bemcgarvey/SAMD21Demo/firmware/MSD-SPI/firmware/src/config/default/peripheral/sercom/spi_master/plib_sercom0_spi_master.c

/*******************************************************************************
  SERIAL COMMUNICATION SERIAL PERIPHERAL INTERFACE(SERCOM0_SPI) PLIB

  Company
    Microchip Technology Inc.

  File Name
    plib_sercom0_spi_master.c

  Summary
    SERCOM0_SPI Master PLIB Implementation File.

  Description
    This file defines the interface to the SERCOM SPI peripheral library.
    This library provides access to and control of the associated
    peripheral instance.

  Remarks:
    None.

*******************************************************************************/

// DOM-IGNORE-BEGIN
/*******************************************************************************
* Copyright (C) 2018 Microchip Technology Inc. and its subsidiaries.
*
* Subject to your compliance with these terms, you may use Microchip software
* and any derivatives exclusively with Microchip products. It is your
* responsibility to comply with third party license terms applicable to your
* use of third party software (including open source software) that may
* accompany Microchip software.
*
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
* IN NO EVENT WILL MICROCHIP BE LIABLE FOR ANY INDIRECT, SPECIAL, PUNITIVE,
* INCIDENTAL OR CONSEQUENTIAL LOSS, DAMAGE, COST OR EXPENSE OF ANY KIND
* WHATSOEVER RELATED TO THE SOFTWARE, HOWEVER CAUSED, EVEN IF MICROCHIP HAS
* BEEN ADVISED OF THE POSSIBILITY OR THE DAMAGES ARE FORESEEABLE. TO THE
* FULLEST EXTENT ALLOWED BY LAW, MICROCHIP'S TOTAL LIABILITY ON ALL CLAIMS IN
* ANY WAY RELATED TO THIS SOFTWARE WILL NOT EXCEED THE AMOUNT OF FEES, IF ANY,
* THAT YOU HAVE PAID DIRECTLY TO MICROCHIP FOR THIS SOFTWARE.
*******************************************************************************/
// DOM-IGNORE-END

#include "interrupts.h"
#include "plib_sercom0_spi_master.h"

// *****************************************************************************
// *****************************************************************************
// Section: MACROS Definitions
// *****************************************************************************
// *****************************************************************************


/* SERCOM0 clk freq value for the baud calculation */
#define SERCOM0_Frequency      (48000000UL)

/* SERCOM0 SPI baud value for 5000000 Hz baud rate */
#define SERCOM0_SPIM_BAUD_VALUE         (3UL)

/*Global object to save SPI Exchange related data  */
static SPI_OBJECT sercom0SPIObj;

// *****************************************************************************
// *****************************************************************************
// Section: SERCOM0_SPI Implementation
// *****************************************************************************
// *****************************************************************************
// *****************************************************************************

// *****************************************************************************
/* Function:
    void SERCOM0_SPI_Initialize(void);

  Summary:
    Initializes instance SERCOM0 of the SERCOM module operating in SPI mode.

  Description:
    This function initializes instance SERCOM0 of SERCOM module operating in SPI mode.
    This function should be called before any other library function. The SERCOM
    module will be configured as per the MHC settings.

  Remarks:
    Refer plib_sercom0_spi.h file for more information.
*/

void SERCOM0_SPI_Initialize(void)
{
    /* Instantiate the SERCOM0 SPI object */
    sercom0SPIObj.callback = NULL ;
    sercom0SPIObj.transferIsBusy = false ;
    sercom0SPIObj.txSize = 0U;
    sercom0SPIObj.rxSize = 0U;

    /* Selection of the Character Size and Receiver Enable */
    SERCOM0_REGS->SPIM.SERCOM_CTRLB = SERCOM_SPIM_CTRLB_CHSIZE_8_BIT | SERCOM_SPIM_CTRLB_RXEN_Msk ;

    /* Wait for synchronization */
    while((SERCOM0_REGS->SPIM.SERCOM_SYNCBUSY) != 0U)
    {
        /* Do nothing */
    }

    /* Selection of the Baud Value */
    SERCOM0_REGS->SPIM.SERCOM_BAUD = (uint8_t)SERCOM_SPIM_BAUD_BAUD(SERCOM0_SPIM_BAUD_VALUE);

    /* Configure Data Out Pin Out , Master Mode,
     * Data In and Pin Out,Data Order and Standby mode if configured
     * and Selection of the Clock Phase and Polarity and Enable the SPI Module
     */
    SERCOM0_REGS->SPIM.SERCOM_CTRLA = SERCOM_SPIM_CTRLA_MODE_SPI_MASTER | SERCOM_SPIM_CTRLA_DOPO_PAD0 | SERCOM_SPIM_CTRLA_DIPO_PAD2 | SERCOM_SPIM_CTRLA_CPOL_IDLE_LOW | SERCOM_SPIM_CTRLA_CPHA_LEADING_EDGE | SERCOM_SPIM_CTRLA_DORD_MSB | SERCOM_SPIM_CTRLA_ENABLE_Msk ;


    /* Wait for synchronization */
    while((SERCOM0_REGS->SPIM.SERCOM_SYNCBUSY) != 0U)
    {
        /* Do nothing */
    }
}

// *****************************************************************************
/* Function:
    bool SERCOM0_SPI_TransferSetup(SPI_TRANSFER_SETUP *setup,
                                                uint32_t spiSourceClock);

 Summary:
    Configure SERCOM SPI operational parameters at run time.

  Description:
    This function allows the application to change the SERCOM SPI operational
    parameter at run time. The application can thus override the MHC defined
    configuration for these parameters. The parameter are specified via the
    SPI_TRANSFER_SETUP type setup parameter. Each member of this parameter
    should be initialized to the desired value.

    The application may feel need to call this function in situation where
    multiple SPI slaves, each with different operation parameters, are connected
    to one SPI master. This function can thus be used to setup the SPI Master to
    meet the communication needs of the slave.

    Calling this function will affect any ongoing communication. The application
    must thus ensure that there is no on-going communication on the SPI before
    calling this function.

  Remarks:
    Refer plib_sercom0_spi.h file for more information.
*/

bool SERCOM0_SPI_TransferSetup(SPI_TRANSFER_SETUP *setup, uint32_t spiSourceClock)
{
    uint32_t baudValue = 0U;

    bool statusValue = false;

    if(spiSourceClock == 0U)
    {
        /* Fetch Master Clock Frequency directly */
        spiSourceClock = SERCOM0_Frequency;
    }

    /* Disable the SPI Module */
    SERCOM0_REGS->SPIM.SERCOM_CTRLA &= ~(SERCOM_SPIM_CTRLA_ENABLE_Msk);

    /* Wait for synchronization */
    while((SERCOM0_REGS->SPIM.SERCOM_SYNCBUSY) != 0U)
    {
        /* Do nothing */
    }

    if(setup != NULL)
    {
        baudValue = (spiSourceClock/(2U*(setup->clockFrequency))) - 1U;

        if((baudValue > 0U) && (baudValue <= 255U))
        {
            /* Selection of the Clock Polarity and Clock Phase */
            SERCOM0_REGS->SPIM.SERCOM_CTRLA &= ~(SERCOM_SPIM_CTRLA_CPOL_Msk | SERCOM_SPIM_CTRLA_CPHA_Msk);
            SERCOM0_REGS->SPIM.SERCOM_CTRLA |= (uint32_t)setup->clockPolarity | (uint32_t)setup->clockPhase;

            /* Selection of the Baud Value */
            SERCOM0_REGS->SPIM.SERCOM_BAUD = (uint8_t)baudValue;

            /* Selection of the Character Size */
            SERCOM0_REGS->SPIM.SERCOM_CTRLB &= ~SERCOM_SPIM_CTRLB_CHSIZE_Msk;
            SERCOM0_REGS->SPIM.SERCOM_CTRLB |= (uint32_t)setup->dataBits;

            /* Wait for synchronization */
            while((SERCOM0_REGS->SPIM.SERCOM_SYNCBUSY) != 0U)
            {
                /* Do nothing */
            }

            statusValue = true;
        }
    }

    /* Enabling the SPI Module */
    SERCOM0_REGS->SPIM.SERCOM_CTRLA |= SERCOM_SPIM_CTRLA_ENABLE_Msk;

    /* Wait for synchronization */
    while((SERCOM0_REGS->SPIM.SERCOM_SYNCBUSY) != 0U)
    {
        /* Do nothing */
    }

    return statusValue;
}


// *****************************************************************************
/* Function:
    void SERCOM0_SPI_CallbackRegister(const SERCOM_SPI_CALLBACK* callBack,
                                                    uintptr_t context);

  Summary:
    Allows application to register callback with PLIB.

  Description:
    This function allows application to register an event handling function
    for the PLIB to call back when requested data exchange operation has
    completed or any error has occurred.
    The callback should be registered before the client performs exchange
    operation.
    At any point if application wants to stop the callback, it can use this
    function with "callBack" value as NULL.

  Remarks:
    Refer plib_sercom0_spi.h file for more information.
*/

void SERCOM0_SPI_CallbackRegister(SERCOM_SPI_CALLBACK callBack, uintptr_t context )
{
    sercom0SPIObj.callback = callBack;

    sercom0SPIObj.context = context;
}

// *****************************************************************************
/* Function:
    bool SERCOM0_SPI_IsBusy(void);

  Summary:
    Returns transfer status of SERCOM SERCOM0SPI.

  Description:
    This function ture if the SERCOM SERCOM0SPI module is busy with a transfer. The
    application can use the function to check if SERCOM SERCOM0SPI module is busy
    before calling any of the data transfer functions. The library does not
    allow a data transfer operation if another transfer operation is already in
    progress.

    This function can be used as an alternative to the callback function when
    the library is operating interrupt mode. The allow the application to
    implement a synchronous interface to the library.

  Remarks:
    Refer plib_sercom0_spi.h file for more information.
*/

bool SERCOM0_SPI_IsBusy(void)
{
    bool isBusy = false;
	if ((sercom0SPIObj.txSize == 0U) && (sercom0SPIObj.rxSize == 0U))
	{
		/* This means no transfer has been requested yet; hence SPI is not busy. */
		isBusy = false;
	}
	else
	{
        /* if transmit is not complete or if the state flag is not set, SPI is busy */
        isBusy = (((SERCOM0_REGS->SPIM.SERCOM_INTFLAG & SERCOM_SPIM_INTFLAG_TXC_Msk) == 0U) || sercom0SPIObj.transferIsBusy);
	}
    return isBusy;
}

bool SERCOM0_SPI_IsTransmitterBusy(void)
{
    return ((SERCOM0_REGS->SPIM.SERCOM_INTFLAG & SERCOM_SPIM_INTFLAG_TXC_Msk) == 0)? true : false;
}

// *****************************************************************************
/* Function:
    bool SERCOM0_SPI_WriteRead (void* pTransmitData, size_t txSize
                                        void* pReceiveData, size_t rxSize);

  Summary:
    Write and Read data on SERCOM SERCOM0 SPI peripheral.

  Description:
    This function transmits "txSize" number of bytes and receives "rxSize"
    number of bytes on SERCOM SERCOM0 SPI module. Data pointed by pTransmitData is
    transmitted and received data is saved in the location pointed by
    pReceiveData. The function will transfer the maximum of "txSize" or "rxSize"
    data units towards completion.

    When "Interrupt Mode" option is unchecked in MHC, this function will be
    blocking in nature.  In this mode, the function will not return until all
    the requested data is transferred.  The function returns true after
    transferring all the data.  This indicates that the operation has been
    completed.

    When "Interrupt Mode" option is selected in MHC, the function will be
    non-blocking in nature.  The function returns immediately. The data transfer
    process continues in the peripheral interrupt.  The application specified
    transmit and receive buffer  are ownerd by the library until the data
    transfer is complete and should not be modified by the application till the
    transfer is complete.  Only one transfer is allowed at any time. The
    Application can use a callback function or a polling function to check for
    completion of the transfer. If a callback is required, this should be
    registered prior to calling the SERCOM0_SPI_WriteRead() function. The
    application can use the SERCOM0_SPI_IsBusy() to poll for completion.

  Remarks:
    Refer plib_sercom0_spi.h file for more information.
*/

bool SERCOM0_SPI_WriteRead (void* pTransmitData, size_t txSize, void* pReceiveData, size_t rxSize)
{
    bool isRequestAccepted = false;
    uint32_t dummyData = 0U;

    /* Verify the request */
    if((((txSize > 0U) && (pTransmitData != NULL)) || ((rxSize > 0U) && (pReceiveData != NULL))) && (sercom0SPIObj.transferIsBusy == false))
    {
        if((SERCOM0_REGS->SPIM.SERCOM_CTRLB & SERCOM_SPIM_CTRLB_CHSIZE_Msk) == (uint32_t)SPI_DATA_BITS_9)
        {
            /* For 9-bit transmission, the txSize and rxSize must be an even number. */
            if(((txSize > 0U) && ((txSize & 0x01U) != 0U)) || ((rxSize > 0U) && ((rxSize & 0x01U) != 0U)))
            {
                return isRequestAccepted;
            }
        }

        isRequestAccepted = true;
        sercom0SPIObj.txBuffer = pTransmitData;
        sercom0SPIObj.rxBuffer = pReceiveData;
        sercom0SPIObj.rxCount = 0U;
        sercom0SPIObj.txCount = 0U;
        sercom0SPIObj.dummySize = 0U;

        if(pTransmitData != NULL)
        {
            sercom0SPIObj.txSize = txSize;
        }
        else
        {
            sercom0SPIObj.txSize = 0U;
        }

        if(pReceiveData != NULL)
        {
            sercom0SPIObj.rxSize = rxSize;
        }
        else
        {
            sercom0SPIObj.rxSize = 0U;
        }

        sercom0SPIObj.transferIsBusy = true;

        /* Flush out any unread data in SPI read buffer */
        while((SERCOM0_REGS->SPIM.SERCOM_INTFLAG & SERCOM_SPIM_INTFLAG_RXC_Msk) == SERCOM_SPIM_INTFLAG_RXC_Msk)
        {
            dummyData = SERCOM0_REGS->SPIM.SERCOM_DATA;
            (void)dummyData;
        }

        SERCOM0_REGS->SPIM.SERCOM_STATUS |= (uint16_t)SERCOM_SPIM_STATUS_BUFOVF_Msk;

        SERCOM0_REGS->SPIM.SERCOM_INTFLAG |= (uint8_t)SERCOM_SPIM_INTFLAG_ERROR_Msk;

        if(sercom0SPIObj.rxSize > sercom0SPIObj.txSize)
        {
            sercom0SPIObj.dummySize = sercom0SPIObj.rxSize - sercom0SPIObj.txSize;
        }

        /* Start the first write here itself, rest will happen in ISR context */
        if((SERCOM0_REGS->SPIM.SERCOM_CTRLB & SERCOM_SPIM_CTRLB_CHSIZE_Msk) == (uint32_t)SPI_DATA_BITS_8)
        {
            if(sercom0SPIObj.txCount < sercom0SPIObj.txSize)
            {
                SERCOM0_REGS->SPIM.SERCOM_DATA = *((uint8_t*)sercom0SPIObj.txBuffer);

                sercom0SPIObj.txCount++;
            }
            else if(sercom0SPIObj.dummySize > 0U)
            {
                SERCOM0_REGS->SPIM.SERCOM_DATA = 0xFFU;

                sercom0SPIObj.dummySize--;
            }
            else
            {
                /* Do nothing */
            }
        }
        else
        {
            sercom0SPIObj.txSize >>= 1U;
            sercom0SPIObj.dummySize >>= 1U;
            sercom0SPIObj.rxSize >>= 1U;

            if(sercom0SPIObj.txCount < sercom0SPIObj.txSize)
            {
                SERCOM0_REGS->SPIM.SERCOM_DATA = *((uint16_t*)sercom0SPIObj.txBuffer) & SERCOM_SPIM_DATA_Msk;

                sercom0SPIObj.txCount++;
            }
            else if(sercom0SPIObj.dummySize > 0U)
            {
                SERCOM0_REGS->SPIM.SERCOM_DATA = 0xFFFFU & SERCOM_SPIM_DATA_Msk;

                sercom0SPIObj.dummySize--;
            }
            else
            {
                /* Do nothing */
            }
        }

        if(rxSize > 0U)
        {
            /* Enable ReceiveComplete  */
            SERCOM0_REGS->SPIM.SERCOM_INTENSET = (uint8_t)SERCOM_SPIM_INTENSET_RXC_Msk;
        }
        else
        {
            /* Enable the DataRegisterEmpty  */
            SERCOM0_REGS->SPIM.SERCOM_INTENSET = (uint8_t)SERCOM_SPIM_INTENSET_DRE_Msk;
        }
    }

    return isRequestAccepted;
}

bool SERCOM0_SPI_Write(void* pTransmitData, size_t txSize)
{
    return SERCOM0_SPI_WriteRead(pTransmitData, txSize, NULL, 0U);
}

bool SERCOM0_SPI_Read(void* pReceiveData, size_t rxSize)
{
    return SERCOM0_SPI_WriteRead(NULL, 0U, pReceiveData, rxSize);
}

// *****************************************************************************
/* Function:
    void SERCOM0_SPI_InterruptHandler(void);

  Summary:
    Handler that handles the SPI interrupts

  Description:
    This Function is called from the handler to handle the exchange based on the
    Interrupts.

  Remarks:
    Refer plib_sercom0_spi.h file for more information.
*/

void SERCOM0_SPI_InterruptHandler(void)
{
    uint32_t dataBits = 0U;
    uint32_t receivedData = 0U;
    static bool isLastByteTransferInProgress = false;

    if(SERCOM0_REGS->SPIM.SERCOM_INTENSET != 0U)
    {
        dataBits = SERCOM0_REGS->SPIM.SERCOM_CTRLB & SERCOM_SPIM_CTRLB_CHSIZE_Msk;

        if((SERCOM0_REGS->SPIM.SERCOM_INTFLAG & SERCOM_SPIM_INTFLAG_RXC_Msk) == SERCOM_SPIM_INTFLAG_RXC_Msk)
        {
            receivedData =  SERCOM0_REGS->SPIM.SERCOM_DATA;

            if(sercom0SPIObj.rxCount < sercom0SPIObj.rxSize)
            {
                if(dataBits == (uint32_t)SPI_DATA_BITS_8)
                {
                    ((uint8_t*)sercom0SPIObj.rxBuffer)[sercom0SPIObj.rxCount++] = (uint8_t)receivedData;
                }
                else
                {
                    ((uint16_t*)sercom0SPIObj.rxBuffer)[sercom0SPIObj.rxCount++] = (uint16_t)receivedData;
                }
            }
        }

        /* If there are more words to be transmitted, then transmit them here and keep track of the count */
        if((SERCOM0_REGS->SPIM.SERCOM_INTFLAG & SERCOM_SPIM_INTFLAG_DRE_Msk) == SERCOM_SPIM_INTFLAG_DRE_Msk)
        {
            /* Disable the DRE interrupt. This will be enabled back if more than
             * one byte is pending to be transmitted */
            SERCOM0_REGS->SPIM.SERCOM_INTENCLR = (uint8_t)SERCOM_SPIM_INTENCLR_DRE_Msk;

            if(dataBits == (uint32_t)SPI_DATA_BITS_8)
            {
                if(sercom0SPIObj.txCount < sercom0SPIObj.txSize)
                {
                    SERCOM0_REGS->SPIM.SERCOM_DATA = ((uint8_t*)sercom0SPIObj.txBuffer)[sercom0SPIObj.txCount++];
                }
                else if(sercom0SPIObj.dummySize > 0U)
                {
                    SERCOM0_REGS->SPIM.SERCOM_DATA = 0xFFU;

                    sercom0SPIObj.dummySize--;
                }
                else
                {
                    /* Do nothing */
                }
            }
            else
            {
                if(sercom0SPIObj.txCount < sercom0SPIObj.txSize)
                {
                    SERCOM0_REGS->SPIM.SERCOM_DATA = ((uint16_t*)sercom0SPIObj.txBuffer)[sercom0SPIObj.txCount++];
                }
                else if(sercom0SPIObj.dummySize > 0U)
                {
                    SERCOM0_REGS->SPIM.SERCOM_DATA = 0xFFFFU;

                    sercom0SPIObj.dummySize--;
                }
                else
                {
                    /* Do nothing */
                }
            }

            if((sercom0SPIObj.txCount == sercom0SPIObj.txSize) && (sercom0SPIObj.dummySize == 0U))
            {
                 /* At higher baud rates, the data in the shift register can be
                 * shifted out and TXC flag can get set resulting in a
                 * callback been given to the application with the SPI interrupt
                 * pending with the application. This will then result in the
                 * interrupt handler being called again with nothing to transmit.
                 * To avoid this, a software flag is set, but
                 * the TXC interrupt is not enabled until the very end.
                 */

                isLastByteTransferInProgress = true;
            }
            else if(sercom0SPIObj.rxCount == sercom0SPIObj.rxSize)
            {
                SERCOM0_REGS->SPIM.SERCOM_INTENSET = (uint8_t)SERCOM_SPIM_INTENSET_DRE_Msk;

                SERCOM0_REGS->SPIM.SERCOM_INTENCLR = (uint8_t)SERCOM_SPIM_INTENCLR_RXC_Msk;
            }
            else
            {
                /* Do nothing */
            }
        }

        if(((SERCOM0_REGS->SPIM.SERCOM_INTFLAG & SERCOM_SPIM_INTFLAG_TXC_Msk) == SERCOM_SPIM_INTFLAG_TXC_Msk) && (isLastByteTransferInProgress == true))
        {
            if(sercom0SPIObj.rxCount == sercom0SPIObj.rxSize)
            {
                sercom0SPIObj.transferIsBusy = false;

                /* Disable the Data Register empty and Receive Complete Interrupt flags */
                SERCOM0_REGS->SPIM.SERCOM_INTENCLR = (uint8_t)(SERCOM_SPIM_INTENCLR_DRE_Msk | SERCOM_SPIM_INTENCLR_RXC_Msk | SERCOM_SPIM_INTENSET_TXC_Msk);

                isLastByteTransferInProgress = false;

                if(sercom0SPIObj.callback != NULL)
                {
                    sercom0SPIObj.callback(sercom0SPIObj.context);
                }
            }
        }

        if(isLastByteTransferInProgress == true)
        {
            /* For the last byte transfer, the DRE interrupt is already disabled.
             * Enable TXC interrupt to ensure no data is present in the shift
             * register before application callback is called.
             */
            SERCOM0_REGS->SPIM.SERCOM_INTENSET = (uint8_t)SERCOM_SPIM_INTENSET_TXC_Msk;
        }
    }
}
