bemcgarvey/SAMD21Demo/firmware/MSD-SPI/firmware/src/config/default/initialization.c

/*******************************************************************************
  System Initialization File

  File Name:
    initialization.c

  Summary:
    This file contains source code necessary to initialize the system.

  Description:
    This file contains source code necessary to initialize the system.  It
    implements the "SYS_Initialize" function, defines the configuration bits,
    and allocates any necessary global system resources,
 *******************************************************************************/

// DOM-IGNORE-BEGIN
/*******************************************************************************
* Copyright (C) 2018 Microchip Technology Inc. and its subsidiaries.
*
* Subject to your compliance with these terms, you may use Microchip software
* and any derivatives exclusively with Microchip products. It is your
* responsibility to comply with third party license terms applicable to your
* use of third party software (including open source software) that may
* accompany Microchip software.
*
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
* IN NO EVENT WILL MICROCHIP BE LIABLE FOR ANY INDIRECT, SPECIAL, PUNITIVE,
* INCIDENTAL OR CONSEQUENTIAL LOSS, DAMAGE, COST OR EXPENSE OF ANY KIND
* WHATSOEVER RELATED TO THE SOFTWARE, HOWEVER CAUSED, EVEN IF MICROCHIP HAS
* BEEN ADVISED OF THE POSSIBILITY OR THE DAMAGES ARE FORESEEABLE. TO THE
* FULLEST EXTENT ALLOWED BY LAW, MICROCHIP'S TOTAL LIABILITY ON ALL CLAIMS IN
* ANY WAY RELATED TO THIS SOFTWARE WILL NOT EXCEED THE AMOUNT OF FEES, IF ANY,
* THAT YOU HAVE PAID DIRECTLY TO MICROCHIP FOR THIS SOFTWARE.
 *******************************************************************************/
// DOM-IGNORE-END

// *****************************************************************************
// *****************************************************************************
// Section: Included Files
// *****************************************************************************
// *****************************************************************************
#include "configuration.h"
#include "definitions.h"
#include "device.h"



// ****************************************************************************
// ****************************************************************************
// Section: Configuration Bits
// ****************************************************************************
// ****************************************************************************
#pragma config NVMCTRL_BOOTPROT = SIZE_0BYTES
#pragma config NVMCTRL_EEPROM_SIZE = SIZE_0BYTES
#pragma config BOD33USERLEVEL = 0x7 // Enter Hexadecimal value
#pragma config BOD33_EN = ENABLED
#pragma config BOD33_ACTION = RESET

#pragma config BOD33_HYST = DISABLED
#pragma config NVMCTRL_REGION_LOCKS = 0xffff // Enter Hexadecimal value

#pragma config WDT_ENABLE = DISABLED
#pragma config WDT_ALWAYSON = DISABLED
#pragma config WDT_PER = CYC16384

#pragma config WDT_WINDOW_0 = SET
#pragma config WDT_WINDOW_1 = 0x4 // Enter Hexadecimal value
#pragma config WDT_EWOFFSET = CYC16384
#pragma config WDT_WEN = DISABLED




// *****************************************************************************
// *****************************************************************************
// Section: Driver Initialization Data
// *****************************************************************************
// *****************************************************************************
// <editor-fold defaultstate="collapsed" desc="DRV_MEMORY Instance 0 Initialization Data">


static DRV_MEMORY_CLIENT_OBJECT gDrvMemory0ClientObject[DRV_MEMORY_CLIENTS_NUMBER_IDX0];

static DRV_MEMORY_BUFFER_OBJECT gDrvMemory0BufferObject[DRV_MEMORY_BUFFER_QUEUE_SIZE_IDX0];

const DRV_MEMORY_DEVICE_INTERFACE drvMemory0DeviceAPI = {
    .Open               = DRV_AT25_Open,
    .Close              = DRV_AT25_Close,
    .Status             = DRV_AT25_Status,
    .SectorErase        = NULL,
    .Read               = DRV_AT25_Read,
    .PageWrite          = DRV_AT25_PageWrite,
    .EventHandlerSet    = NULL,
    .GeometryGet        = (DRV_MEMORY_DEVICE_GEOMETRY_GET)DRV_AT25_GeometryGet,
    .TransferStatusGet  = (DRV_MEMORY_DEVICE_TRANSFER_STATUS_GET)DRV_AT25_TransferStatusGet
};

const DRV_MEMORY_INIT drvMemory0InitData =
{
    .memDevIndex                = DRV_AT25_INDEX,
    .memoryDevice               = &drvMemory0DeviceAPI,
    .isMemDevInterruptEnabled   = false,
    .isFsEnabled                = false,
    .ewBuffer                   = NULL,
    .clientObjPool              = (uintptr_t)&gDrvMemory0ClientObject[0],
    .bufferObj                  = (uintptr_t)&gDrvMemory0BufferObject[0],
    .queueSize                  = DRV_MEMORY_BUFFER_QUEUE_SIZE_IDX0,
    .nClientsMax                = DRV_MEMORY_CLIENTS_NUMBER_IDX0
};

// </editor-fold>
// <editor-fold defaultstate="collapsed" desc="DRV_AT25 Initialization Data">

/* SPI PLIB Interface Initialization for AT25 Driver */
const DRV_AT25_PLIB_INTERFACE drvAT25PlibAPI = {

    /* SPI PLIB WriteRead function */
    .writeRead = (DRV_AT25_PLIB_WRITE_READ)SERCOM0_SPI_WriteRead,

    /* SPI PLIB Write function */
    .write = (DRV_AT25_PLIB_WRITE)SERCOM0_SPI_Write,

    /* SPI PLIB Read function */
    .read = (DRV_AT25_PLIB_READ)SERCOM0_SPI_Read,

    /* SPI PLIB Transfer Status function */
    .isBusy = (DRV_AT25_PLIB_IS_BUSY)SERCOM0_SPI_IsBusy,

    /* SPI PLIB Callback Register */
    .callbackRegister = (DRV_AT25_PLIB_CALLBACK_REGISTER)SERCOM0_SPI_CallbackRegister,
};

/* AT25 Driver Initialization Data */
const DRV_AT25_INIT drvAT25InitData =
{
    /* SPI PLIB API  interface*/
    .spiPlib = &drvAT25PlibAPI,

    /* AT25 Number of clients */
    .numClients = DRV_AT25_CLIENTS_NUMBER_IDX,

    /* EEPROM Page Size in bytes */
    .pageSize = DRV_AT25_EEPROM_PAGE_SIZE,

    /* Total size of the EEPROM in bytes */
    .flashSize = DRV_AT25_EEPROM_FLASH_SIZE,

    .blockStartAddress =    0x0,

    .chipSelectPin    = DRV_AT25_CHIP_SELECT_PIN_IDX,

    .holdPin    = DRV_AT25_HOLD_PIN_IDX,

    .writeProtectPin    = DRV_AT25_WP_PIN_IDX,
};

// </editor-fold>


// *****************************************************************************
// *****************************************************************************
// Section: System Data
// *****************************************************************************
// *****************************************************************************
/* Structure to hold the object handles for the modules in the system. */
SYSTEM_OBJECTS sysObj;

// *****************************************************************************
// *****************************************************************************
// Section: Library/Stack Initialization Data
// *****************************************************************************
// *****************************************************************************
/******************************************************
 * USB Driver Initialization
 ******************************************************/
 
/*  When designing a Self-powered USB Device, the application should make sure
    that USB_DEVICE_Attach() function is called only when VBUS is actively powered.
	Therefore, the firmware needs some means to detect when the Host is powering 
	the VBUS. A 5V tolerant I/O pin can be connected to VBUS (through a resistor)
	and can be used to detect when VBUS is high or low. The application can specify
	a VBUS Detect function through the USB Driver Initialize data structure. 
	The USB device stack will periodically call this function. If the VBUS is 
	detected, the USB_DEVICE_EVENT_POWER_DETECTED event is generated. If the VBUS 
	is removed (i.e., the device is physically detached from Host), the USB stack 
	will generate the event USB_DEVICE_EVENT_POWER_REMOVED. The application should 
	call USB_DEVICE_Detach() when VBUS is removed. 
    
    The following are the steps to generate the VBUS_SENSE Function through MHC     
        1) Navigate to MHC->Tools->Pin Configuration and Configure the pin used 
		   as VBUS_SENSE. Set this pin Function as "GPIO" and set as "Input". 
		   Provide a custom name to the pin.
        2) Select the USB Driver Component in MHC Project Graph and enable the  
		   "Enable VBUS Sense" Check-box.     
        3) Specify the custom name of the VBUS SENSE pin in the "VBUS SENSE Pin Name" box.  */ 
static DRV_USB_VBUS_LEVEL DRV_USBFSV1_VBUS_Comparator(void)
{
    DRV_USB_VBUS_LEVEL retVal = DRV_USB_VBUS_LEVEL_INVALID;
    
    if(true == USB_VBUS_SENSE_Get())
    {
        retVal = DRV_USB_VBUS_LEVEL_VALID;
    }
	return (retVal);

}


const DRV_USBFSV1_INIT drvUSBInit =
{
    /* Interrupt Source for USB module */ 
    .interruptSource = USB_IRQn,

    /* System module initialization */
    .moduleInit = {0},

    /* USB Controller to operate as USB Device */
    .operationMode = DRV_USBFSV1_OPMODE_DEVICE,

    /* USB Full Speed Operation */
	.operationSpeed = USB_SPEED_FULL,
    
    /* Stop in idle */
    .runInStandby = true,

    /* Suspend in sleep */
    .suspendInSleep = false,

    /* Identifies peripheral (PLIB-level) ID */
    .usbID = USB_REGS,
	
    /* Function to check for VBus */
    .vbusComparator = DRV_USBFSV1_VBUS_Comparator
	
};




// *****************************************************************************
// *****************************************************************************
// Section: System Initialization
// *****************************************************************************
// *****************************************************************************



// *****************************************************************************
// *****************************************************************************
// Section: Local initialization functions
// *****************************************************************************
// *****************************************************************************



/*******************************************************************************
  Function:
    void SYS_Initialize ( void *data )

  Summary:
    Initializes the board, services, drivers, application and other modules.

  Remarks:
 */

void SYS_Initialize ( void* data )
{

    NVMCTRL_REGS->NVMCTRL_CTRLB = NVMCTRL_CTRLB_RWS(3UL);

  
    PORT_Initialize();

    CLOCK_Initialize();




    NVMCTRL_Initialize( );

    EVSYS_Initialize();

    SERCOM0_SPI_Initialize();


    sysObj.drvMemory0 = DRV_MEMORY_Initialize((SYS_MODULE_INDEX)DRV_MEMORY_INDEX_0, (SYS_MODULE_INIT *)&drvMemory0InitData);

    sysObj.drvAT25 = DRV_AT25_Initialize(DRV_AT25_INDEX, (SYS_MODULE_INIT *)&drvAT25InitData);




	 /* Initialize the USB device layer */
    sysObj.usbDevObject0 = USB_DEVICE_Initialize (USB_DEVICE_INDEX_0 , ( SYS_MODULE_INIT* ) & usbDevInitData);
	
	

	/* Initialize USB Driver */ 
    sysObj.drvUSBFSV1Object = DRV_USBFSV1_Initialize(DRV_USBFSV1_INDEX_0, (SYS_MODULE_INIT *) &drvUSBInit);	


    APP_Initialize();


    NVIC_Initialize();

}


/*******************************************************************************
 End of File
*/
